brunohorta82/BH_PZEM_ESP8266/caixas/img1.png

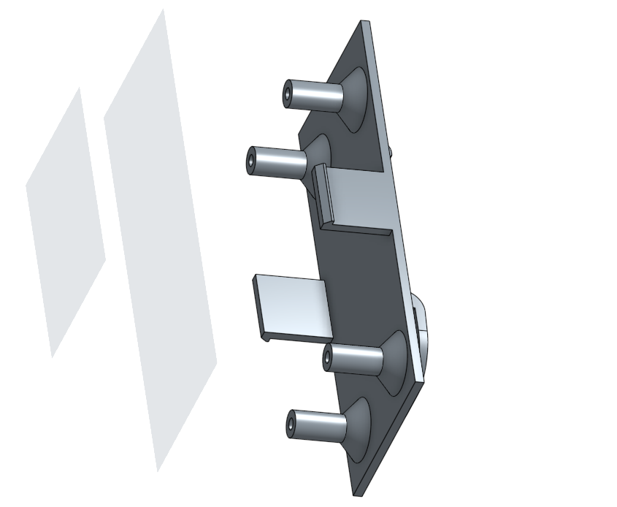
caixas/img1.png
