brunohorta82/BH_PZEM_ESP8266/caixas/img2.png

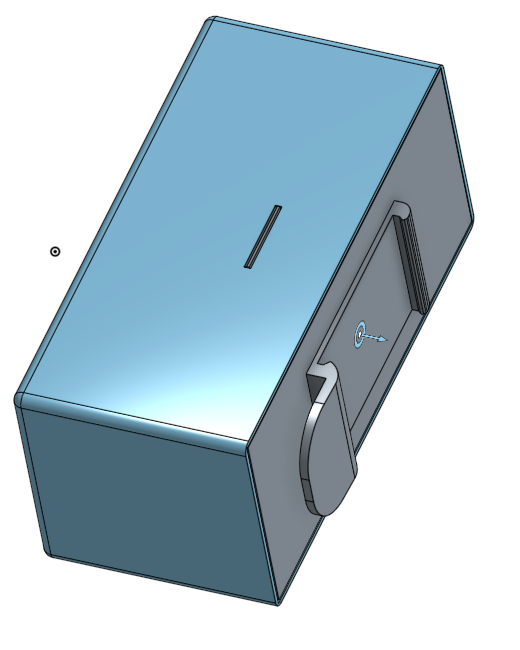
caixas/img2.png
