brunohorta82/BH_PZEM_ESP8266/caixas/img3.png

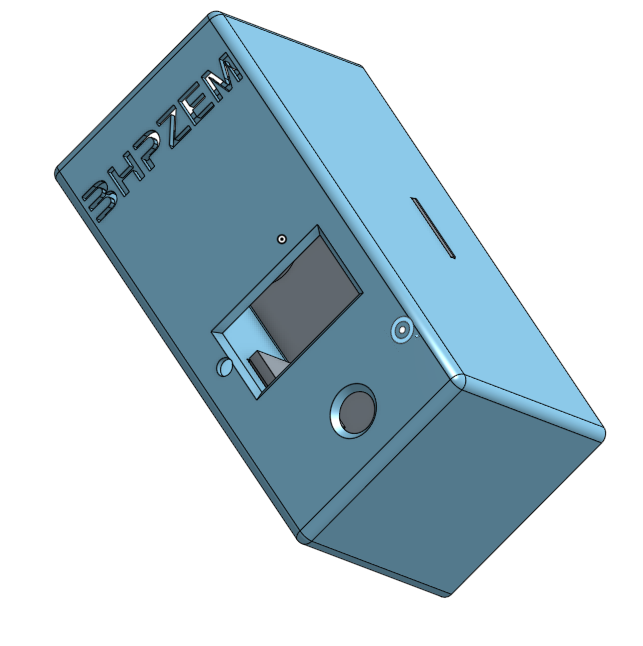
caixas/img3.png
