brunohorta82/BH_PZEM_ESP8266/images/IMG_4421.JPG

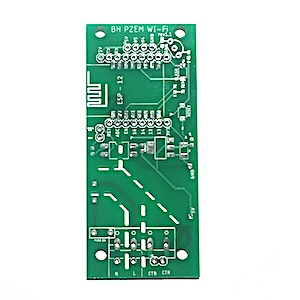
images/IMG_4421.JPG
