brunohorta82/BH_PZEM_ESP8266/Firmware/BH_EASY_IOT_PZEM/WebServer.ino

#include "AsyncJson.h"
#include "ArduinoJson.h"
#include "StaticSite.h"
#include "StaticCss.h"
#include "StaticJs.h"

// SKETCH BEGIN
AsyncWebServer server(80);

void  setupWebserver(){
  MDNS.begin(getHostname().c_str());
  MDNS.addService("bhsystems","tcp",80);
  MDNS.addServiceTxt("bhsystems", "tcp", "nodeId", getConfigJson().get<String>("nodeId"));
  MDNS.addServiceTxt("bhsystems", "tcp", "config_version", getConfigJson().get<String>("configVersion"));
  MDNS.addServiceTxt("bhsystems", "tcp", "hardwareId", String(ESP.getChipId()));
  MDNS.addServiceTxt("bhsystems", "tcp", "wifi-signal",  String(WiFi.RSSI()));

  MDNS.addServiceTxt("bhsystems", "tcp", "type",  String(FACTORY_TYPE));

  server.addHandler(&events);
  /** HTML  **/
  server.on("/", HTTP_GET, [](AsyncWebServerRequest *request){
    AsyncWebServerResponse *response = request->beginResponse_P(200, "text/html", index_html,sizeof(index_html));
    response->addHeader("Content-Encoding", "gzip");
    request->send(response);
  });
  
server.on("/scan", HTTP_GET, [](AsyncWebServerRequest *request){
    activateScan();
    request->send(200,  "application/json","{\"result\":\"OK\"}");
  });
  
  server.on("/dashboard.html", HTTP_GET, [](AsyncWebServerRequest *request){
    AsyncWebServerResponse *response = request->beginResponse_P(200, "text/html", dashboard_html,sizeof(dashboard_html));
    response->addHeader("Content-Encoding", "gzip");
    request->send(response);
  });
  
 
    server.on("/pzem-readings", HTTP_GET, [](AsyncWebServerRequest *request){
    AsyncResponseStream *response = request->beginResponseStream("application/json");
    getPzemReadings().printTo(*response);
    request->send(response);
  });
  server.on("/emoncms.html", HTTP_GET, [](AsyncWebServerRequest *request){
    AsyncWebServerResponse *response = request->beginResponse_P(200, "text/html", emoncms_html,sizeof(emoncms_html));
    response->addHeader("Content-Encoding", "gzip");
    request->send(response);
  });

  server.on("/firmware.html", HTTP_GET, [](AsyncWebServerRequest *request){
    AsyncWebServerResponse *response = request->beginResponse_P(200, "text/html", firmware_html,sizeof(firmware_html));
    response->addHeader("Content-Encoding", "gzip");
    request->send(response);
  });
  server.on("/homeassistant.html", HTTP_GET, [](AsyncWebServerRequest *request){
    AsyncWebServerResponse *response = request->beginResponse_P(200, "text/html", homeassistant_html,sizeof(homeassistant_html));
    response->addHeader("Content-Encoding", "gzip");
    request->send(response);
  });

  server.on("/mqtt.html", HTTP_GET, [](AsyncWebServerRequest *request){
    AsyncWebServerResponse *response = request->beginResponse_P(200, "text/html", mqtt_html,sizeof(mqtt_html));
    response->addHeader("Content-Encoding", "gzip");
    request->send(response);
  });
  server.on("/node.html", HTTP_GET, [](AsyncWebServerRequest *request){
    AsyncWebServerResponse *response = request->beginResponse_P(200, "text/html", node_html,sizeof(node_html));
    response->addHeader("Content-Encoding", "gzip");
    request->send(response);
  });
  server.on("/wifi.html", HTTP_GET, [](AsyncWebServerRequest *request){
    AsyncWebServerResponse *response = request->beginResponse_P(200, "text/html", wifi_html,sizeof(wifi_html));
    response->addHeader("Content-Encoding", "gzip");
    request->send(response);
  });
   

  /** JS    **/

  server.on("/js/GaugeMeter.js", HTTP_GET, [](AsyncWebServerRequest *request){
    AsyncWebServerResponse *response = request->beginResponse_P(200, "application/js", GaugeMeter_js,sizeof(GaugeMeter_js));
    response->addHeader("Content-Encoding", "gzip");
    response->addHeader("Expires","Mon, 1 Jan 2222 10:10:10 GMT");
    request->send(response);
  });

  server.on("/js/index.js", HTTP_GET, [](AsyncWebServerRequest *request){
    AsyncWebServerResponse *response = request->beginResponse_P(200, "application/js", index_js,sizeof(index_js));
    response->addHeader("Content-Encoding", "gzip");
    response->addHeader("Expires","Mon, 1 Jan 2222 10:10:10 GMT");
    request->send(response);
  });
  server.on("/js/jquery.min.js", HTTP_GET, [](AsyncWebServerRequest *request){
    AsyncWebServerResponse *response = request->beginResponse_P(200, "application/js", jquery_min_js,sizeof(jquery_min_js));
    response->addHeader("Content-Encoding", "gzip");
    response->addHeader("Expires","Mon, 1 Jan 2222 10:10:10 GMT");
    request->send(response);
  });
   
  /** CSS   **/
  server.on("/css/AdminLTE.min.css", HTTP_GET, [](AsyncWebServerRequest *request){
    AsyncWebServerResponse *response = request->beginResponse_P(200, "text/css", AdminLTE_min_css,sizeof(AdminLTE_min_css));
    response->addHeader("Content-Encoding", "gzip");
    response->addHeader("Expires","Mon, 1 Jan 2222 10:10:10 GMT");
    request->send(response);
  });

  
 server.on("/config", HTTP_GET, [](AsyncWebServerRequest *request){
  AsyncResponseStream *response = request->beginResponseStream("application/json");
  getConfigJson().printTo(*response);
  request->send(response);
  });
   
   server.on("/wifi-status", HTTP_GET, [](AsyncWebServerRequest *request){
   AsyncResponseStream *response = request->beginResponseStream("application/json");
  if(!request->host().equals("192.168.4.1") && WiFi.getMode() & WIFI_AP){
    dissableAP();
  }
  wifiJSONStatus().printTo(*response);
  request->send(response);
  });
  

    
   
  
   server.on("/dissableAP", HTTP_GET, [](AsyncWebServerRequest *request){
   dissableAP();
     request->send(200);
   });
  
   
   server.on("/reboot", HTTP_GET, [](AsyncWebServerRequest *request){
   shouldReboot = true;
   request->redirect("/");
  });

   server.on("/loaddefaults", HTTP_GET, [](AsyncWebServerRequest *request){
   request->send(200 );
   laodDefaults = true;
  });
   server.on("/auto-update", HTTP_GET, [](AsyncWebServerRequest *request){
   request->send(200 );
   autoUpdate = true;
  });
  


  AsyncCallbackJsonWebHandler* handlerNode = new AsyncCallbackJsonWebHandler("/save-node", [](AsyncWebServerRequest *request, JsonVariant &json) {
    JsonObject& jsonObj = json.as<JsonObject>();
    if (jsonObj.success()) {
      AsyncResponseStream *response = request->beginResponseStream("application/json");
      //SAVE CONFIG
      saveNode(jsonObj).printTo(*response);
      request->send(response);
    } else {
      logger("[WEBSERVER] Json Error");
      request->send(400, "text/plain", "JSON INVALID");
    }
});server.addHandler(handlerNode);
  
    AsyncCallbackJsonWebHandler* handlerWifi = new AsyncCallbackJsonWebHandler("/save-wifi", [](AsyncWebServerRequest *request, JsonVariant &json) {
    JsonObject& jsonObj = json.as<JsonObject>();
    if (jsonObj.success()) {
      AsyncResponseStream *response = request->beginResponseStream("application/json");
      //SAVE CONFIG
      saveWifi(jsonObj).printTo(*response);
      
      request->send(response);
    } else {
      logger("[WEBSERVER] Json Error");
      request->send(400, "text/plain", "JSON INVALID");
    }
});server.addHandler(handlerWifi);


    AsyncCallbackJsonWebHandler* handlerAdopt = new AsyncCallbackJsonWebHandler("/adopt-controller-config", [](AsyncWebServerRequest *request, JsonVariant &json) {
    JsonObject& jsonObj = json.as<JsonObject>();
    if (jsonObj.success()) {
      AsyncResponseStream *response = request->beginResponseStream("application/json");
      //SAVE CONFIG
      adoptControllerConfig(jsonObj).printTo(*response);
      
      request->send(response);
    } else {
      logger("[WEBSERVER] Json Error");
      request->send(400, "text/plain", "JSON INVALID");
    }
});server.addHandler(handlerAdopt);

     AsyncCallbackJsonWebHandler* handlerha = new AsyncCallbackJsonWebHandler("/save-ha", [](AsyncWebServerRequest *request, JsonVariant &json) {
    JsonObject& jsonObj = json.as<JsonObject>();
    if (jsonObj.success()) {
      AsyncResponseStream *response = request->beginResponseStream("application/json");
      //SAVE CONFIG
      saveHa(jsonObj).printTo(*response);
      
      request->send(response);
    } else {
      logger("[WEBSERVER] Json Error");
      request->send(400, "text/plain", "JSON INVALID");
    }
});server.addHandler(handlerha ); 

AsyncCallbackJsonWebHandler* handleremon = new AsyncCallbackJsonWebHandler("/save-emoncms", [](AsyncWebServerRequest *request, JsonVariant &json) {
    JsonObject& jsonObj = json.as<JsonObject>();
    if (jsonObj.success()) {
      AsyncResponseStream *response = request->beginResponseStream("application/json");
      //SAVE CONFIG
      saveEmoncms(jsonObj).printTo(*response);
      
      request->send(response);
    } else {
      logger("[WEBSERVER] Json Error");
      request->send(400, "text/plain", "JSON INVALID");
    }
});server.addHandler(handleremon ); 

    AsyncCallbackJsonWebHandler* handlermqtt = new AsyncCallbackJsonWebHandler("/save-mqtt", [](AsyncWebServerRequest *request, JsonVariant &json) {
    JsonObject& jsonObj = json.as<JsonObject>();
    if (jsonObj.success()) {
      AsyncResponseStream *response = request->beginResponseStream("application/json");
      //SAVE CONFIG
      saveMqtt(jsonObj).printTo(*response);
      
      request->send(response);
    } else {
      logger("[WEBSERVER] Json Error");
      request->send(400, "text/plain", "JSON INVALID");
    }
});server.addHandler(handlermqtt );

 
  server.on("/update", HTTP_POST, [](AsyncWebServerRequest *request){
    shouldReboot = !Update.hasError();
    AsyncWebServerResponse *response = request->beginResponse(200, "text/html", shouldReboot? "<!DOCTYPE html><html lang=\"en\"><head> <meta charset=\"UTF-8\"> <title>Atualização</title> <style>body{background-color: rgb(34, 34, 34); color: white; font-size: 18px; padding: 10px; font-weight: lighter;}</style> <script type=\"text/javascript\">function Redirect(){window.location=\"/\";}document.write(\"Atualização com sucesso, vai ser redirecionado automaticamente daqui a 20 segundos. Aguarde...\"); setTimeout('Redirect()', 20000); </script></head><body></body></html>":"<!DOCTYPE html><html lang=\"en\"><head> <meta charset=\"UTF-8\"> <title>Atualização</title> <style>body{background-color: #cc0000; color: white; font-size: 18px; padding: 10px; font-weight: lighter;}</style> <script type=\"text/javascript\">function Redirect(){window.location=\"/\";}document.write(\"Atualização falhou, poderá ser necessário fazer reset manualmente ao equipamento e tentar novamente.\"); setTimeout('Redirect()', 10000); </script></head><body></body></html>");
    response->addHeader("Connection", "close");
    request->send(response);
  },[](AsyncWebServerRequest *request, String filename, size_t index, uint8_t *data, size_t len, bool final){
    if(!index){
      logger("[FIRMWARE] Update Start:"+ filename);
      Update.runAsync(true);
      if(!Update.begin((ESP.getFreeSketchSpace() - 0x1000) & 0xFFFFF000)){
        Update.printError(Serial);
      }
    }
    if(!Update.hasError()){
      if(Update.write(data, len) != len){
        Update.printError(Serial);
      }
    }
    if(final){
      if(Update.end(true)){
        logger("[FIRMWARE] Update Success: "+String( index+len));
      } else {
        Update.printError(Serial);
      }
    }
  });
 
  server.onNotFound([](AsyncWebServerRequest *request) {
  
  if (request->method() == HTTP_OPTIONS) {
    request->send(200);
  } else {
    request->send(404);
  }
});
DefaultHeaders::Instance().addHeader(F("Access-Control-Allow-Origin"), F("*"));
DefaultHeaders::Instance().addHeader(F("Access-Control-Allow-Methods"), F("PUT, GET"));
DefaultHeaders::Instance().addHeader(F("Access-Control-Allow-Headers"), F("Content-Type, Origin, Referer, User-Agent"));
  server.begin();
}


void publishOnEventSource(String topic, String payload){
   events.send(payload.c_str(), topic.c_str());
}
void publishOnEventSource(String topic, JsonObject& payloadJson){
    String payload ="";
    payloadJson.printTo(payload);
   events.send(payload.c_str(), topic.c_str());
}
