brunohorta82/BH_PZEM_ESP8266/Firmware/BH_EASY_IOT_PZEM/StaticCss.h

//                _           _       _   _______ ______             _                     
//       /\      | |         (_)     | | |__   __|  ____|           (_)                    
//      /  \   __| |_ __ ___  _ _ __ | |    | |  | |__     _ __ ___  _ _ __    ___ ___ ___ 
//     / /\ \ / _` | '_ ` _ \| | '_ \| |    | |  |  __|   | '_ ` _ \| | '_ \  / __/ __/ __|
//    / ____ \ (_| | | | | | | | | | | |____| |  | |____ _| | | | | | | | | || (__\__ \__ \
//   /_/    \_\__,_|_| |_| |_|_|_| |_|______|_|  |______(_)_| |_| |_|_|_| |_(_)___|___/___/
//                                                                                         
//                                                                                         
const uint8_t AdminLTE_min_css[] PROGMEM={0x1F, 0x8B, 0x08, 0x08, 0xE7, 0x41, 0x46, 0x5C, 0x04, 0x03, 0x41, 0x64, 0x6D, 0x69, 0x6E, 0x4C, 
0x54, 0x45, 0x2E, 0x6D, 0x69, 0x6E, 0x2E, 0x63, 0x73, 0x73, 0x00, 0xC4, 0x1D, 0x77, 0xB3, 0xFA, 
0x36, 0xEC, 0xAB, 0xA4, 0xED, 0xF5, 0xBA, 0x02, 0x0D, 0x1B, 0x1E, 0xD7, 0x5E, 0xF7, 0xB8, 0xEB, 
0xBA, 0x8E, 0xEB, 0x1F, 0x5D, 0x17, 0x48, 0x80, 0xB4, 0x81, 0x50, 0x12, 0xBA, 0x28, 0xDF, 0xBD, 
0xF2, 0x94, 0x6D, 0xD9, 0x21, 0xD0, 0xF5, 0x7B, 0xF7, 0x7B, 0x2F, 0x91, 0x64, 0xD9, 0x96, 0x87, 
0x6C, 0x49, 0x76, 0xFA, 0xAB, 0xEA, 0xB7, 0xDE, 0xAA, 0xCA, 0x7E, 0x7F, 0x4A, 0x37, 0x4D, 0x7E, 
0x8A, 0xF9, 0xFB, 0xBA, 0xDA, 0xEF, 0xF3, 0x43, 0x53, 0x47, 0xE6, 0x9B, 0x49, 0xB0, 0xA9, 0x2A, 
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
0xD0, 0x8D, 0x40, 0x16, 0xA7, 0x62, 0x23, 0xD2, 0xD5, 0xC5, 0x1F, 0xF9, 0xD3, 0x60, 0x7C, 0xFC, 
0x6D, 0xC9, 0xB2, 0xEE, 0xA9, 0x11, 0xD0, 0x1F, 0x0F, 0xE7, 0x93, 0xD9, 0x60, 0x3C, 0x5A, 0xAE, 
0xAB, 0xB2, 0x3A, 0x3D, 0x3D, 0x37, 0x1A, 0x8D, 0x96, 0x2B, 0xE8, 0x99, 0xAC, 0x42, 0x87, 0xAC, 
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
