brunohorta82/BH_PZEM_ESP8266/Firmware/BH_EASY_IOT_PZEM/StaticJs.h

const uint8_t index_js[] PROGMEM={0x1F, 0x8B, 0x08, 0x08, 0xD8, 0xB6, 0x43, 0x5C, 0x04, 0x03, 0x69, 0x6E, 0x64, 0x65, 0x78, 0x2E, 
0x6A, 0x73, 0x00, 0xED, 0x1D, 0x5D, 0x57, 0xEB, 0x44, 0xF0, 0x9D, 0x5F, 0xB1, 0xC6, 0x8F, 0xB4, 
0x4A, 0x4B, 0x41, 0xEF, 0x55, 0x41, 0xF4, 0x20, 0x70, 0x15, 0x15, 0x8A, 0x80, 0x7A, 0x54, 0x3C, 
0x9C, 0xD0, 0x6C, 0x69, 0x34, 0x4D, 0x6A, 0x92, 0xC2, 0x45, 0xBD, 0x4F, 0x3E, 0x78, 0xFC, 0x17, 
0x7A, 0x7C, 0xF0, 0xE8, 0xAB, 0x6F, 0x3E, 0xCA, 0x1F, 0x73, 0x66, 0x3F, 0xB2, 0x9B, 0xAF, 0x26, 
0x29, 0x85, 0x56, 0x0F, 0x3D, 0xE7, 0x5E, 0x9A, 0xCD, 0xCC, 0xCE, 0xEC, 0xCC, 0xEC, 0xEC, 0xEC, 
0xEC, 0x47, 0x7B, 0xBE, 0x17, 0x46, 0x84, 0x7A, 0xF6, 0xC8, 0x77, 0xBC, 0x88, 0x6C, 0x92, 0xEF, 
0x97, 0x08, 0x7C, 0xCE, 0xAD, 0x90, 0x7E, 0x12, 0xB8, 0xEB, 0xC4, 0x30, 0x96, 0x9E, 0x6D, 0x2C, 
0x2D, 0x71, 0xB0, 0xA1, 0x35, 0x8A, 0x21, 0x0C, 0x28, 0xEA, 0x3B, 0x17, 0x06, 0x82, 0x2C, 0xF3, 
0x92, 0x91, 0x1F, 0x51, 0xAF, 0xE7, 0x58, 0x58, 0xF6, 0x99, 0x15, 0x85, 0xB2, 0xDC, 0x1A, 0x8E, 
0x68, 0x60, 0x5D, 0xD0, 0x21, 0xBE, 0xD8, 0xC2, 0x07, 0x1A, 0xBF, 0xBB, 0xF4, 0xDD, 0x48, 0xBE, 
0xFA, 0x14, 0xBE, 0xC7, 0x2F, 0x22, 0x3A, 0x1C, 0x61, 0xE1, 0xE9, 0xB8, 0xD3, 0x79, 0x77, 0x6B, 
0x1B, 0x8A, 0x25, 0xD5, 0xC8, 0xB2, 0xFD, 0x00, 0x5F, 0x7D, 0xF3, 0xD9, 0x00, 0xB9, 0x53, 0xCC, 
0x9D, 0x38, 0x91, 0x4B, 0xC3, 0xAA, 0x2C, 0x1E, 0xFA, 0xD1, 0xCD, 0x9F, 0xF8, 0x90, 0xCB, 0xE7, 
0xB6, 0x1F, 0x04, 0xD4, 0x8B, 0x68, 0x1E, 0xA3, 0x27, 0xD4, 0x0B, 0x6F, 0x7E, 0xF3, 0x75, 0x56, 
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
0xC5, 0xE2, 0x9B, 0xD1, 0x46, 0xC3, 0x5E, 0x7C, 0xFF, 0xD3, 0xCF, 0xB4, 0x51, 0x22, 0xDD, 0x24, 
0x60, 0x0F, 0x20, 0xBC, 0x9D, 0x57, 0x79, 0x11, 0xDD, 0x84, 0x6B, 0x91, 0xAD, 0xAA, 0xCB, 0xE8, 
0x24, 0xAC, 0xF2, 0xA7, 0x45, 0x91, 0xDC, 0xD9, 0x2D, 0x68, 0x3A, 0x93, 0xCB, 0xF1, 0xD0, 0x7E, 
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
