brunohorta82/BH_PZEM_ESP8266/Firmware/BH_EASY_IOT_PZEM/StaticSite.h

const uint8_t emoncms_html[] PROGMEM={0x1F, 0x8B, 0x08, 0x08, 0x83, 0xA3, 0x40, 0x5C, 0x04, 0x03, 0x65, 0x6D, 0x6F, 0x6E, 0x63, 0x6D, 
0x73, 0x2E, 0x68, 0x74, 0x6D, 0x6C, 0x00, 0xB5, 0x54, 0x51, 0x6E, 0xDB, 0x30, 0x0C, 0xBD, 0x0A, 
0xA1, 0xAF, 0xF6, 0xC3, 0x4B, 0xD2, 0x2C, 0x69, 0x32, 0x24, 0x06, 0x82, 0xA1, 0x18, 0x86, 0xB5, 
0x6B, 0xD0, 0xAD, 0x07, 0x90, 0x25, 0x3A, 0x16, 0x26, 0x9B, 0x9E, 0x2C, 0x37, 0xCE, 0x79, 0xF6, 
0xB1, 0x83, 0xF4, 0x62, 0xA3, 0xEB, 0x64, 0x59, 0xE4, 0xFD, 0x04, 0x68, 0x3F, 0x24, 0x4B, 0x7C, 
0x14, 0xC9, 0xF7, 0x2C, 0x71, 0xA1, 0xCD, 0x13, 0x28, 0x2B, 0xAB, 0x6A, 0x29, 0x12, 0x6A, 0x80, 
0x47, 0x54, 0x3A, 0x93, 0x4B, 0xB7, 0x13, 0x31, 0x04, 0x68, 0x94, 0xA1, 0xD4, 0xE8, 0x60, 0x6B, 
0x7C, 0x16, 0x25, 0xE4, 0x78, 0xDD, 0x3A, 0x65, 0xE3, 0x7F, 0x7D, 0xBC, 0xF1, 0x16, 0xD9, 0x7C, 
0x73, 0x77, 0xFF, 0xF5, 0xE3, 0xDD, 0x37, 0x58, 0x0C, 0xB2, 0x71, 0xCC, 0x33, 0x87, 0x8A, 0x17, 
0x29, 0xB9, 0x1C, 0x78, 0x97, 0x1A, 0xB4, 0xBA, 0x42, 0x0F, 0x46, 0x2F, 0x45, 0x9A, 0x0A, 0xD0, 
0xA6, 0x92, 0x89, 0x45, 0xDD, 0xCB, 0xC9, 0x79, 0x74, 0x58, 0x8A, 0xA3, 0x6D, 0x60, 0x51, 0x64, 
0xA3, 0x5C, 0x47, 0x53, 0x68, 0x17, 0x4D, 0x15, 0x8D, 0xAE, 0x02, 0x87, 0x36, 0x71, 0xB4, 0x71, 
0x54, 0x97, 0x2D, 0x60, 0x65, 0x82, 0x16, 0xD8, 0xB6, 0x14, 0x98, 0x53, 0xA1, 0xF2, 0xEA, 0xD1, 
0x59, 0x11, 0xAF, 0xD6, 0x9F, 0xE1, 0xF1, 0xE1, 0x76, 0x31, 0x78, 0xC1, 0xD9, 0xCF, 0x14, 0x65, 
0xED, 0x4F, 0x42, 0x28, 0x2A, 0xBC, 0x23, 0x2B, 0xA0, 0x90, 0x39, 0x9E, 0x9C, 0x06, 0xBF, 0x2B, 
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
0x02, 0xF1, 0x24, 0xB7, 0xA5, 0x6E, 0xDA, 0x9F, 0xA6, 0x60, 0x14, 0x0F, 0xBE, 0x6B, 0x0B, 0xEE, 
0xA2, 0xC1, 0xE0, 0x78, 0xDE, 0x70, 0xB0, 0xFE, 0xB1, 0x64, 0xC4, 0x65, 0x79, 0xFC, 0x08, 0xEA, 
0x46, 0xC7, 0x8A, 0xE6, 0xFC, 0x0A, 0xE6, 0xF1, 0x6B, 0x38, 0x3A, 0x2E, 0x0A, 0xF2, 0x1E, 0x5E, 
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
